crexodon/LED-Window-MatrixV2/Software/Mesh_Root/src/udp.c

#include "udp.h"
#include "mdf_common.h"
#include "mwifi.h"

#include "globals.h"
#include "ota.h"

// example UDP command in bash for setting LEDs:    echo -ne "\x7c\x9e\xbd\xf4\xdd\x84\x01\x00\x00\xFF\x00\xFF\x00\xFF\x00\x00\xFF\xAF\x00\x00\x00\x00" | nc -u -w0 192.168.1.73 7715
// example UDP command in bash for triggering OTA:  echo -ne "\x00\x00\x00\x00\x00\x00\x65http://192.168.1.118:8080/mesh_node.bin\x00" | nc -u -w0 192.168.1.73 7715

void udpReceiveCallback(uint8_t *payload, size_t payloadLen, struct sockaddr_storage sourceAddr) {
    ledPayload_t* packet = (ledPayload_t*)payload;
    size_t dataLen = payloadLen - ledPayloadHeaderSize;

    switch (packet->command) {
        case CMD_OTA:
            // update url is contained in packet data, has to be sent with trailing null byte!
            // also the file has to have the same name as the project ("TAG"), because it's identified by that
            otaStart((char*)packet->data);
            break;

        default: {  // forward everything else to nodes
            mwifi_data_type_t data_type = {0x0};
            data_type.custom = packet->command;

            // place dummy value in data, if no additional payload is given, otherwise mwifi_write throws an error
            const void *dataToSend = dataLen > 0 ? packet->data : &packet->command; 
            dataLen = dataLen > 0 ? dataLen : 1;

            mdf_err_t ret = mwifi_root_write(packet->mac, 1, &data_type, dataToSend, dataLen, false);
        }
    }
}

// UDP server from IDF example
static void udp_server_task(void *pvParameters)
{
    char rx_buffer[128];
    char addr_str[128];
    int addr_family = (int)pvParameters;
    int ip_protocol = 0;
    struct sockaddr_in6 dest_addr;

    while (1) {

        if (addr_family == AF_INET) {
            struct sockaddr_in *dest_addr_ip4 = (struct sockaddr_in *)&dest_addr;
            dest_addr_ip4->sin_addr.s_addr = htonl(INADDR_ANY);
            dest_addr_ip4->sin_family = AF_INET;
            dest_addr_ip4->sin_port = htons(UDP_PORT);
            ip_protocol = IPPROTO_IP;
        } else if (addr_family == AF_INET6) {
            bzero(&dest_addr.sin6_addr.un, sizeof(dest_addr.sin6_addr.un));
            dest_addr.sin6_family = AF_INET6;
            dest_addr.sin6_port = htons(UDP_PORT);
            ip_protocol = IPPROTO_IPV6;
        }

        int sock = socket(addr_family, SOCK_DGRAM, ip_protocol);
        if (sock < 0) {
            ESP_LOGE(TAG, "Unable to create socket: errno %d", errno);
            break;
        }
        ESP_LOGI(TAG, "Socket created");

#if defined(CONFIG_EXAMPLE_IPV4) && defined(CONFIG_EXAMPLE_IPV6)
        if (addr_family == AF_INET6) {
            // Note that by default IPV6 binds to both protocols, it is must be disabled
            // if both protocols used at the same time (used in CI)
            int opt = 1;
            setsockopt(sock, SOL_SOCKET, SO_REUSEADDR, &opt, sizeof(opt));
            setsockopt(sock, IPPROTO_IPV6, IPV6_V6ONLY, &opt, sizeof(opt));
        }
#endif

        int err = bind(sock, (struct sockaddr *)&dest_addr, sizeof(dest_addr));
        if (err < 0) {
            ESP_LOGE(TAG, "Socket unable to bind: errno %d", errno);
        }
        ESP_LOGI(TAG, "Socket bound, port %d", UDP_PORT);

        while (1) {

            ESP_LOGI(TAG, "Waiting for data");
            struct sockaddr_storage source_addr; // Large enough for both IPv4 or IPv6
            socklen_t socklen = sizeof(source_addr);
            int len = recvfrom(sock, rx_buffer, sizeof(rx_buffer) - 1, 0, (struct sockaddr *)&source_addr, &socklen);

            // Error occurred during receiving
            if (len < 0) {
                ESP_LOGE(TAG, "recvfrom failed: errno %d", errno);
                break;
            }
            // Data received
            else {
                // Get the sender's ip address as string
                if (source_addr.ss_family == PF_INET) {
                    inet_ntoa_r(((struct sockaddr_in *)&source_addr)->sin_addr, addr_str, sizeof(addr_str) - 1);
                } else if (source_addr.ss_family == PF_INET6) {
                    inet6_ntoa_r(((struct sockaddr_in6 *)&source_addr)->sin6_addr, addr_str, sizeof(addr_str) - 1);
                }

                rx_buffer[len] = 0; // Null-terminate whatever we received and treat like a string...
                ESP_LOGI(TAG, "Received %d bytes from %s:", len, addr_str);
                ESP_LOGI(TAG, "%s", rx_buffer);

                // int err = sendto(sock, rx_buffer, len, 0, (struct sockaddr *)&source_addr, sizeof(source_addr));
                // if (err < 0) {
                //     ESP_LOGE(TAG, "Error occurred during sending: errno %d", errno);
                //     break;
                // }
                udpReceiveCallback((uint8_t*)rx_buffer, len, source_addr);
            }
        }

        if (sock != -1) {
            ESP_LOGE(TAG, "Shutting down socket and restarting...");
            shutdown(sock, 0);
            close(sock);
        }
    }
    vTaskDelete(NULL);
}

void udpInit() {
    xTaskCreate(udp_server_task, "udp_server", 4096, (void*)AF_INET, 5, NULL);
}
