crexodon/LED-Window-MatrixV2/Software/Mesh_Node/src/led.c

#include "led.h"

#include "mdf_common.h"

#include "driver/rmt.h"
#include "led_strip.h"
#include "globals.h"

led_strip_t *strip;

void ledInit() {
    rmt_config_t config = RMT_DEFAULT_CONFIG_TX(LED_PIN, RMT_TX_CHANNEL);
    // set counter clock to 40MHz
    config.clk_div = 2;

    ESP_ERROR_CHECK(rmt_config(&config));
    ESP_ERROR_CHECK(rmt_driver_install(config.channel, 0, 0));

    // install ws2812 driver
    led_strip_config_t strip_config = LED_STRIP_DEFAULT_CONFIG(LED_NUM, (led_strip_dev_t)config.channel);
    strip = led_strip_new_rmt_ws2812(&strip_config);
    if (!strip) {
        ESP_LOGE(TAG, "install WS2812 driver failed");
    }
    // Clear LED strip (turn off all LEDs)
    ESP_ERROR_CHECK(strip->clear(strip, 100));

    // test data
    ESP_ERROR_CHECK(strip->set_pixel(strip, 0, 255, 0, 0));
    ESP_ERROR_CHECK(strip->set_pixel(strip, 1, 0, 255, 0));
    ESP_ERROR_CHECK(strip->set_pixel(strip, 2, 0, 0, 255));
    ESP_ERROR_CHECK(strip->refresh(strip, 100));

}

void ledSetData(uint8_t *data, size_t len) {
    if (strip) {
        for (int i = 0; i < len; i += 3) {
            int pixelIdx = i / 3;
            ESP_ERROR_CHECK(strip->set_pixel(strip, pixelIdx, data[i], data[i+1], data[i+2]));
        }
        ESP_ERROR_CHECK(strip->refresh(strip, 100));
    }
}
